ColasGael/Color-Pen-Prediction/electronic_board/PCB_results/printed-circuit_front.JPG

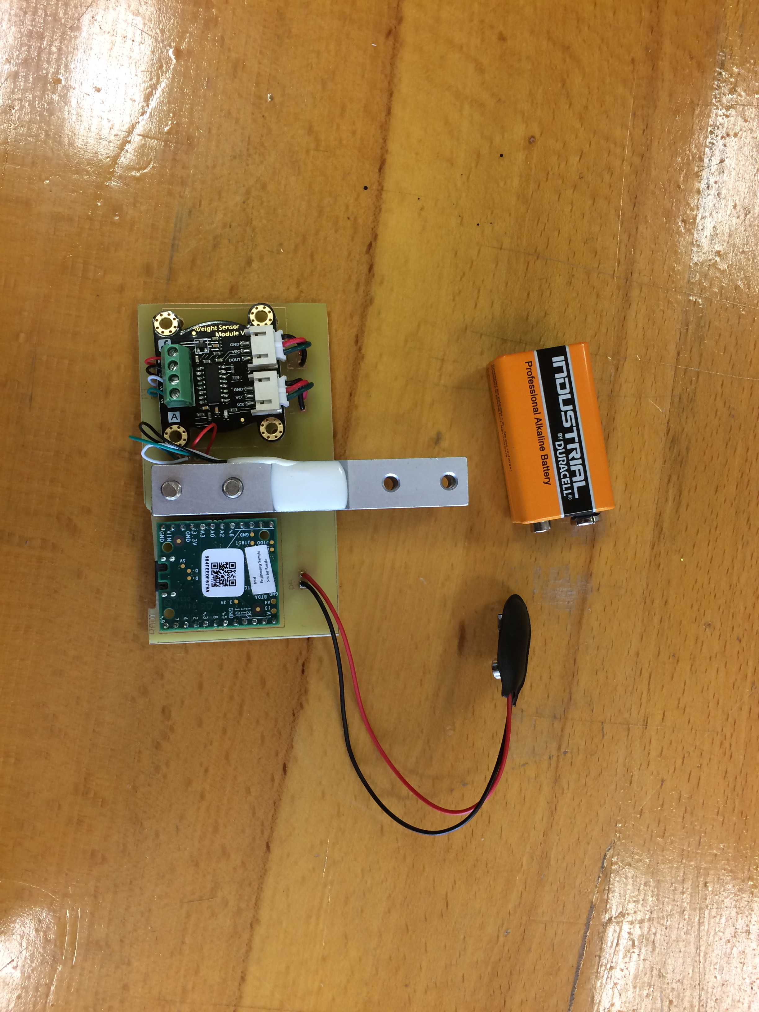
electronic_board/PCB_results/printed-circuit_front.JPG
