ColasGael/Color-Pen-Prediction/electronic_board/PCB_results/printed-circuit_back.JPG

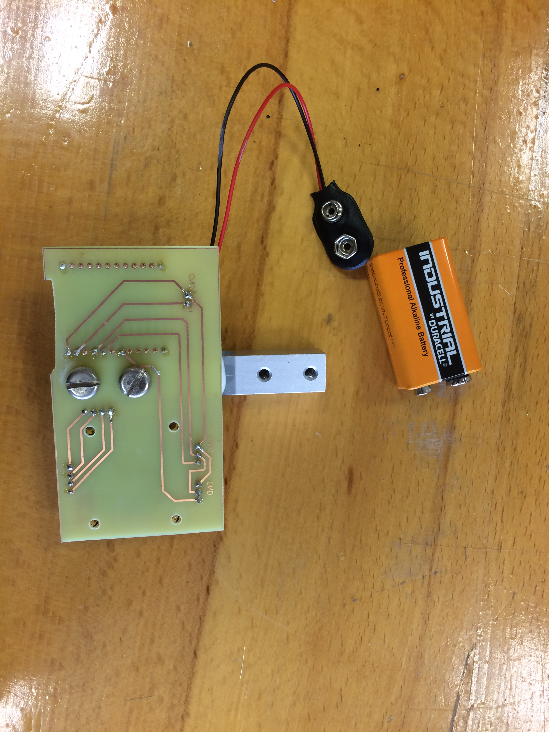
electronic_board/PCB_results/printed-circuit_back.JPG
