ColasGael/Color-Pen-Prediction/electronic_board/PCB_results/PCB_back.JPG

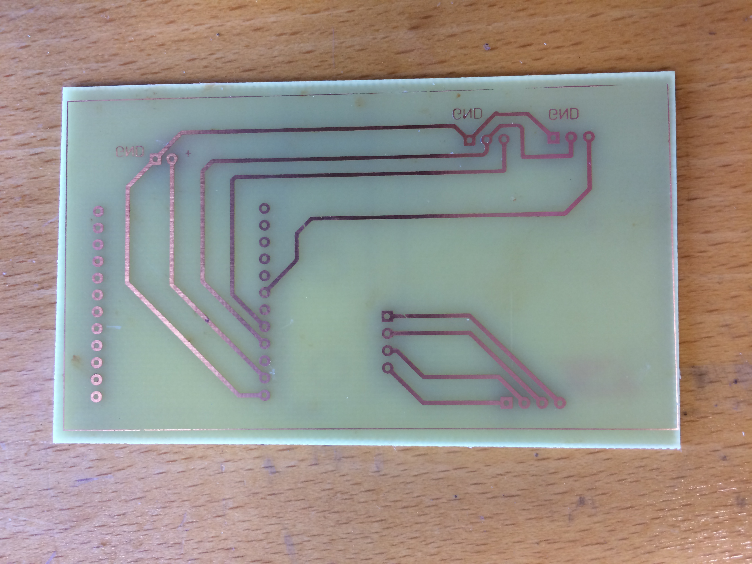
electronic_board/PCB_results/PCB_back.JPG
